mxgxw/reaccion/dsn/auxiliar/Prototipo0/Prototipo0-BreadBoard_bb.png

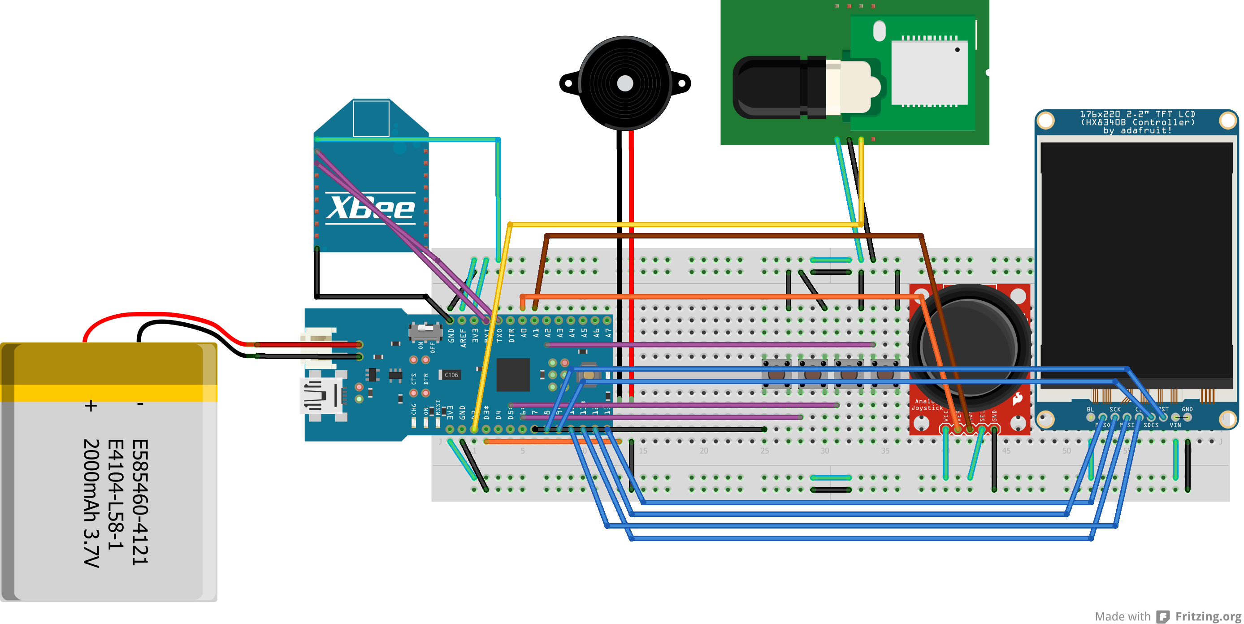
dsn/auxiliar/Prototipo0/Prototipo0-BreadBoard_bb.png
