mxgxw/reaccion/dsn/auxiliar/Prototipo0/Prototipo0-BreadBoard_esquema.png

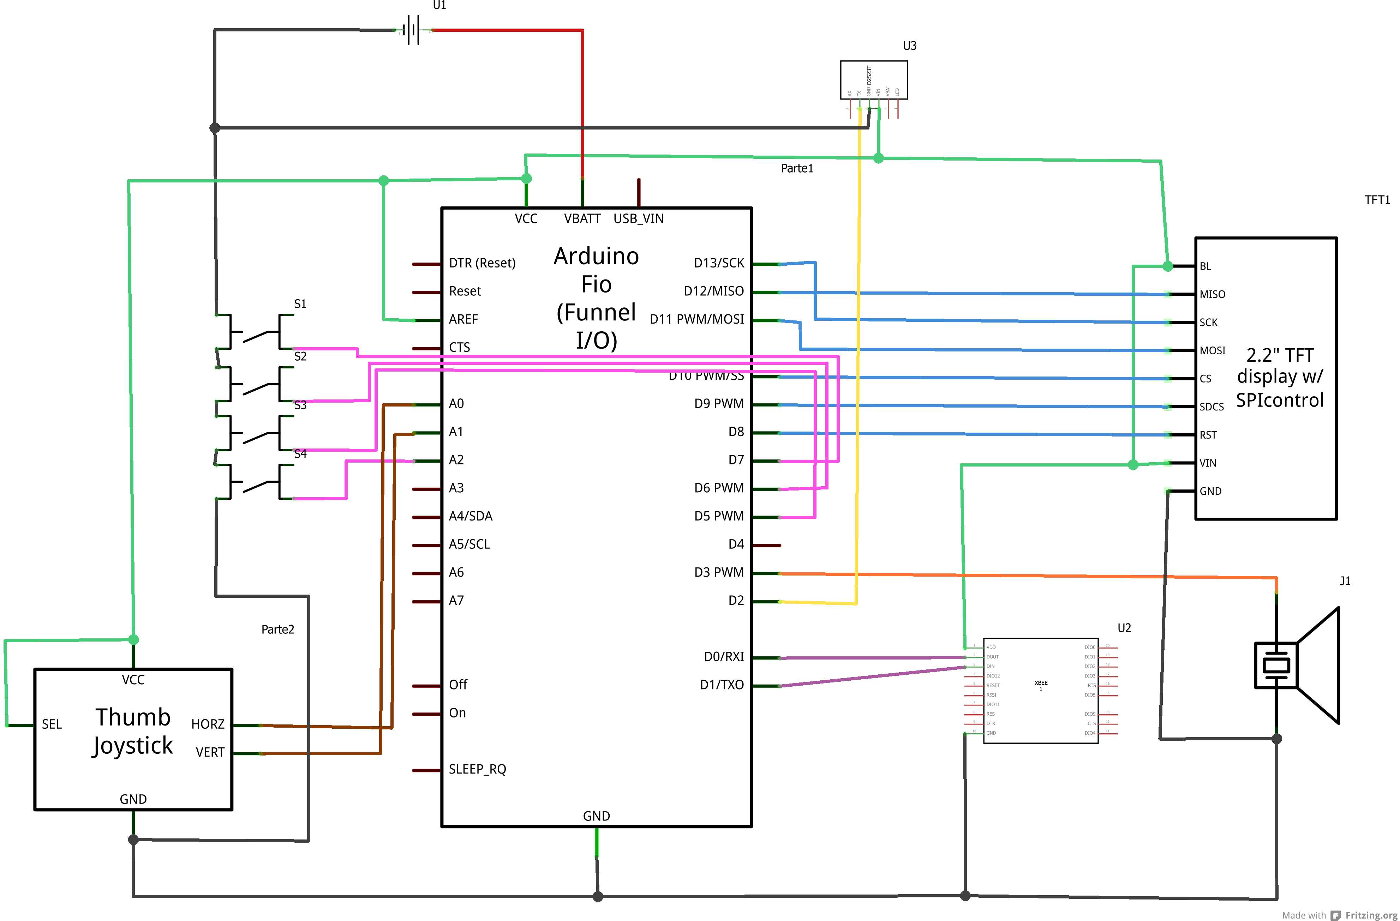
dsn/auxiliar/Prototipo0/Prototipo0-BreadBoard_esquema.png
