mxgxw/reaccion/dsn/main/Renders/Reaccion-01-BoardBottom.png

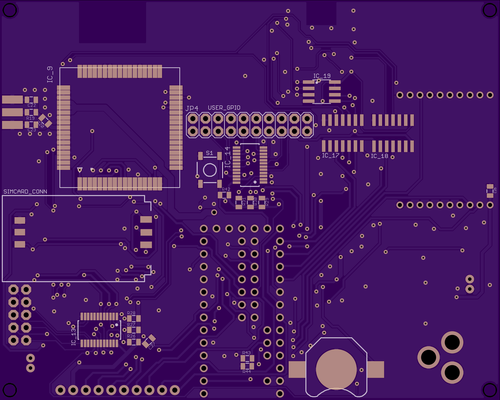
dsn/main/Renders/Reaccion-01-BoardBottom.png
