mxgxw/reaccion/dsn/main/Renders/Reaccion-04-TopLayer.png

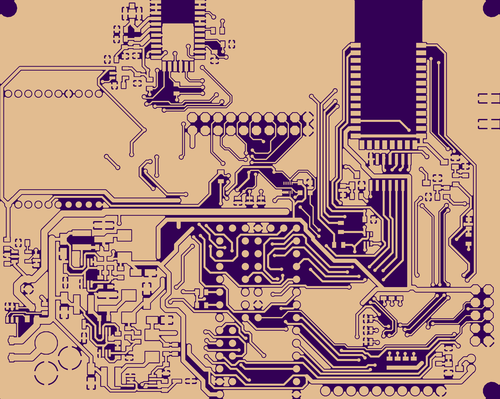
dsn/main/Renders/Reaccion-04-TopLayer.png
