mxgxw/reaccion/dsn/main/Renders/Reaccion-07-TopSilkScreen.png

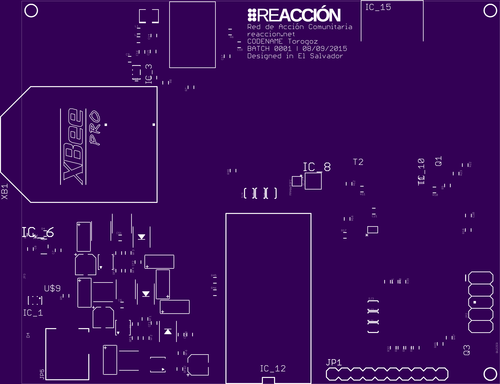
dsn/main/Renders/Reaccion-07-TopSilkScreen.png
