mxgxw/reaccion/extra/Graficos/0_skylab_20120524174805.jpg

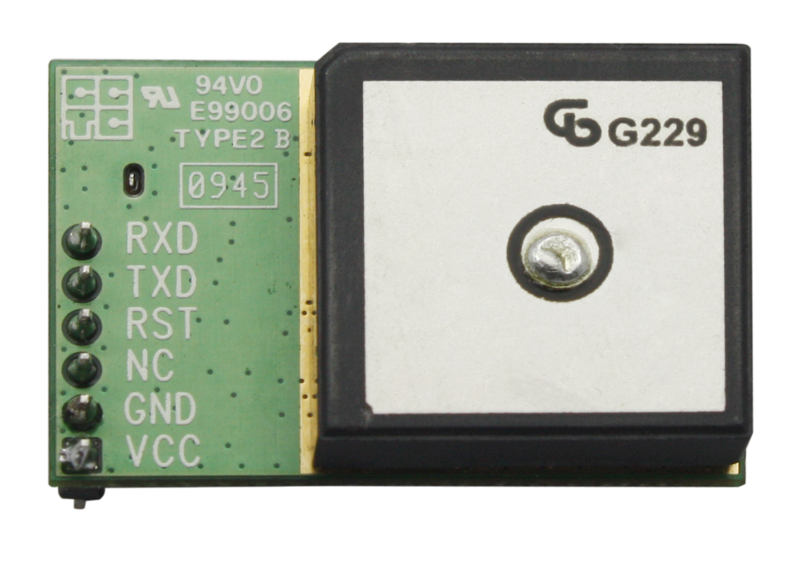
extra/Graficos/0_skylab_20120524174805.jpg
