mxgxw/reaccion/extra/Graficos/09099-01-L.jpg

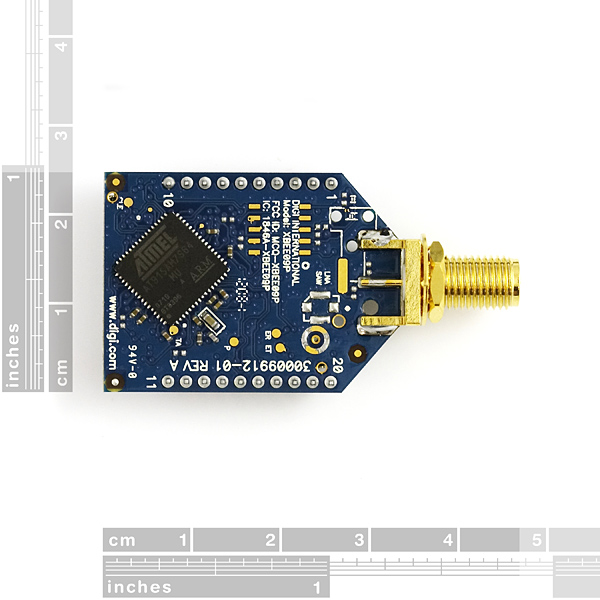
extra/Graficos/09099-01-L.jpg
