mxgxw/reaccion/extra/Graficos/board_top.png

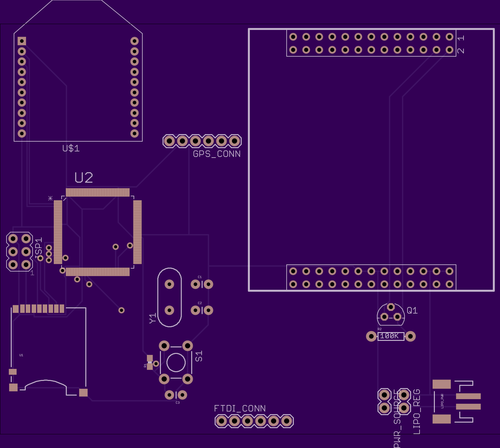
extra/Graficos/board_top.png
