mxgxw/reaccion/extra/Graficos/ET-AVR_Stamp_ATMega128_D.jpg

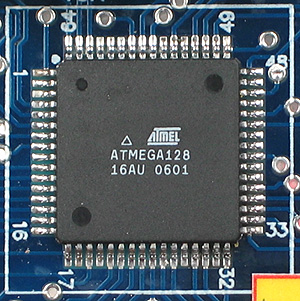
extra/Graficos/ET-AVR_Stamp_ATMega128_D.jpg
