mxgxw/reaccion/extra/Graficos/g3386.bmp

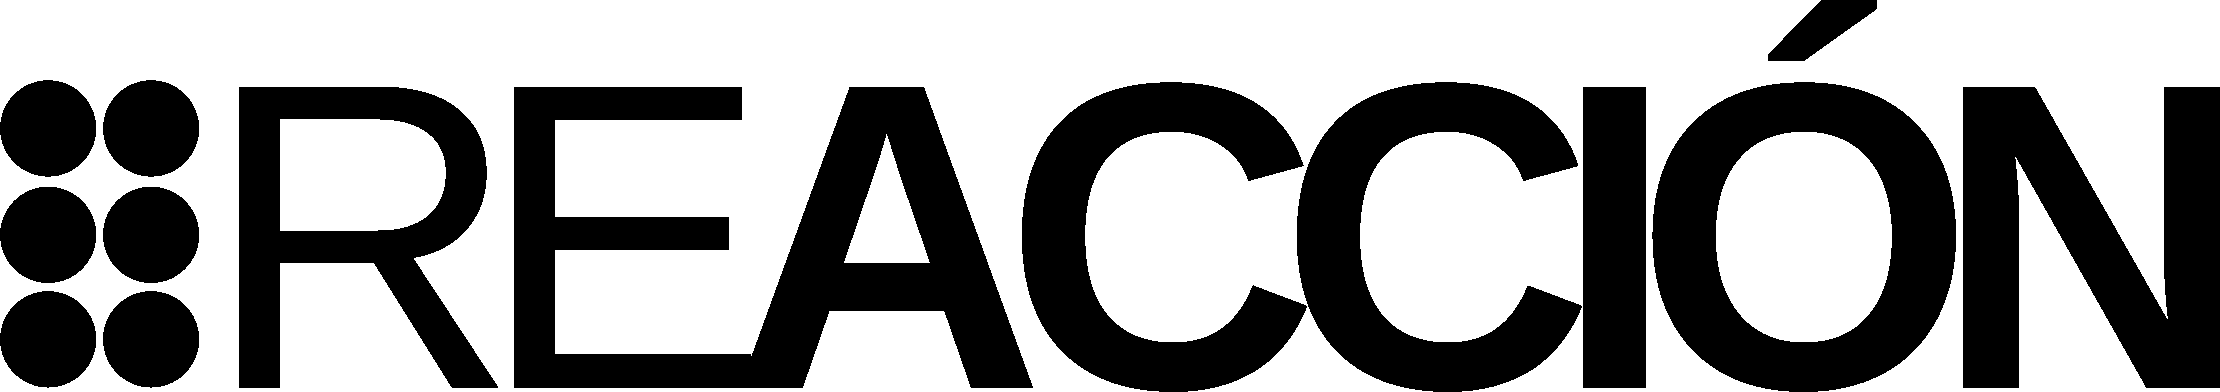
extra/Graficos/g3386.bmp
