mxgxw/reaccion/extra/Graficos/PARA WEB-Finales/1.jpg.png

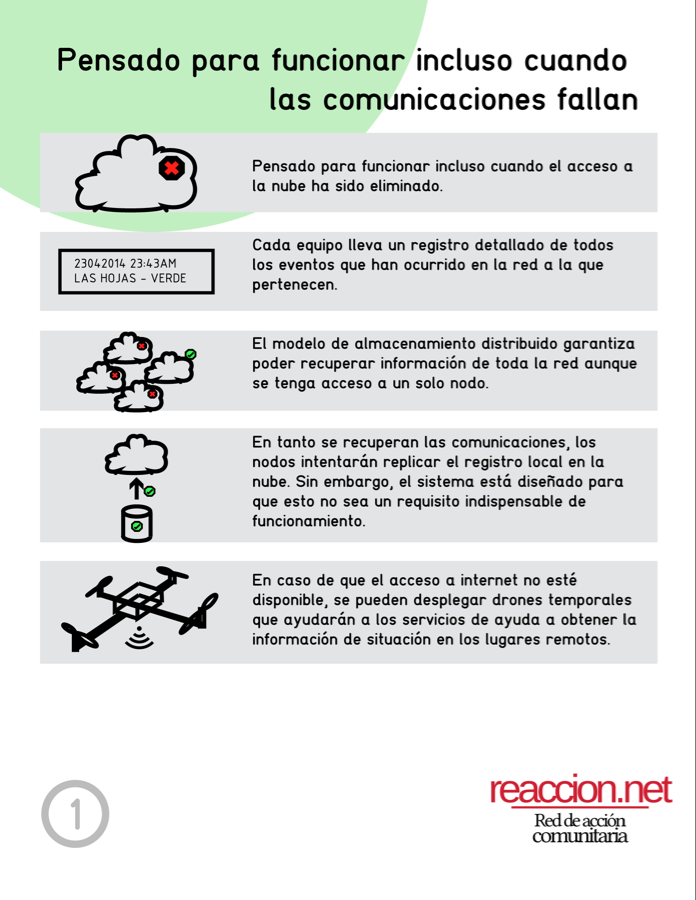
extra/Graficos/PARA WEB-Finales/1.jpg.png
