mxgxw/reaccion/extra/Graficos/PARA WEB-Finales/2.jpg.png

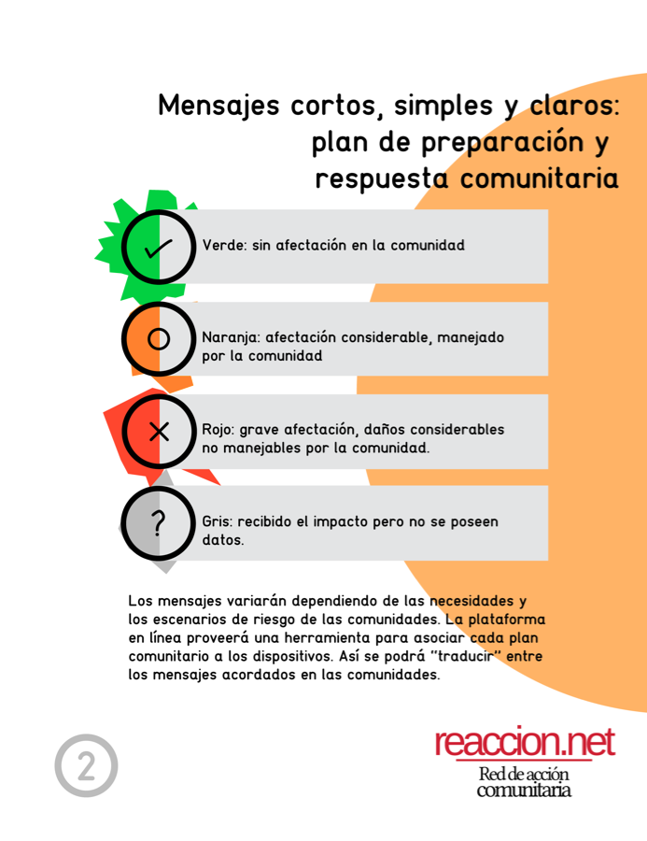
extra/Graficos/PARA WEB-Finales/2.jpg.png
