mxgxw/reaccion/extra/Graficos/PARA WEB-Finales/3.jpg.png

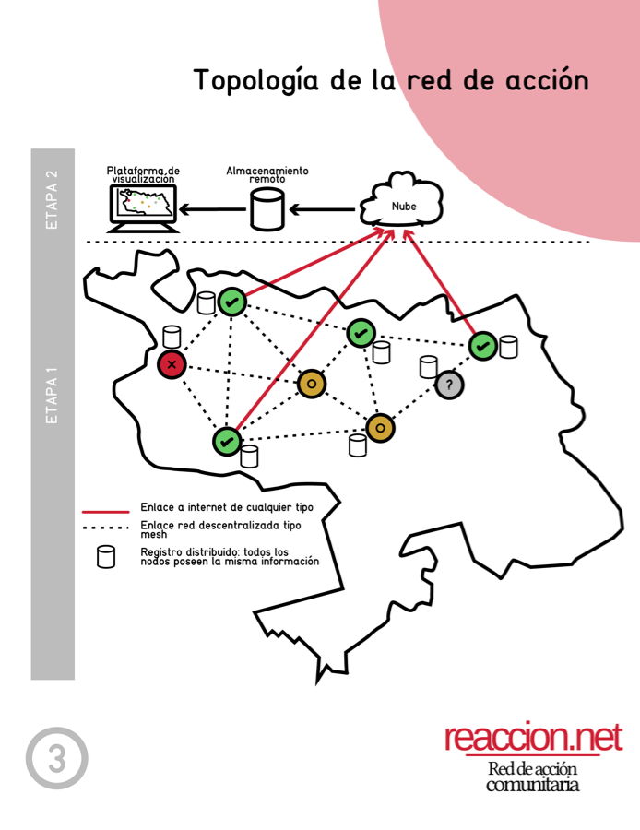
extra/Graficos/PARA WEB-Finales/3.jpg.png
