mxgxw/reaccion/extra/Graficos/PARA WEB-Finales/4.jpg

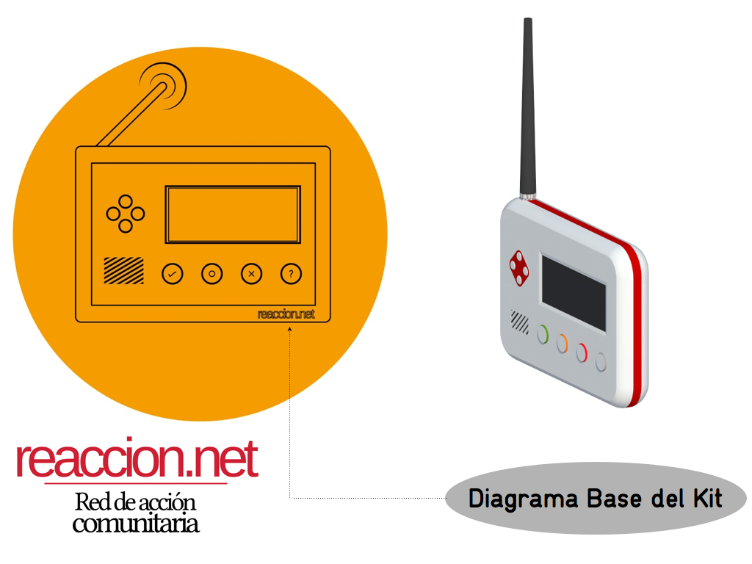
extra/Graficos/PARA WEB-Finales/4.jpg
