mxgxw/reaccion/extra/Graficos/PARA WEB-Finales/5.jpg

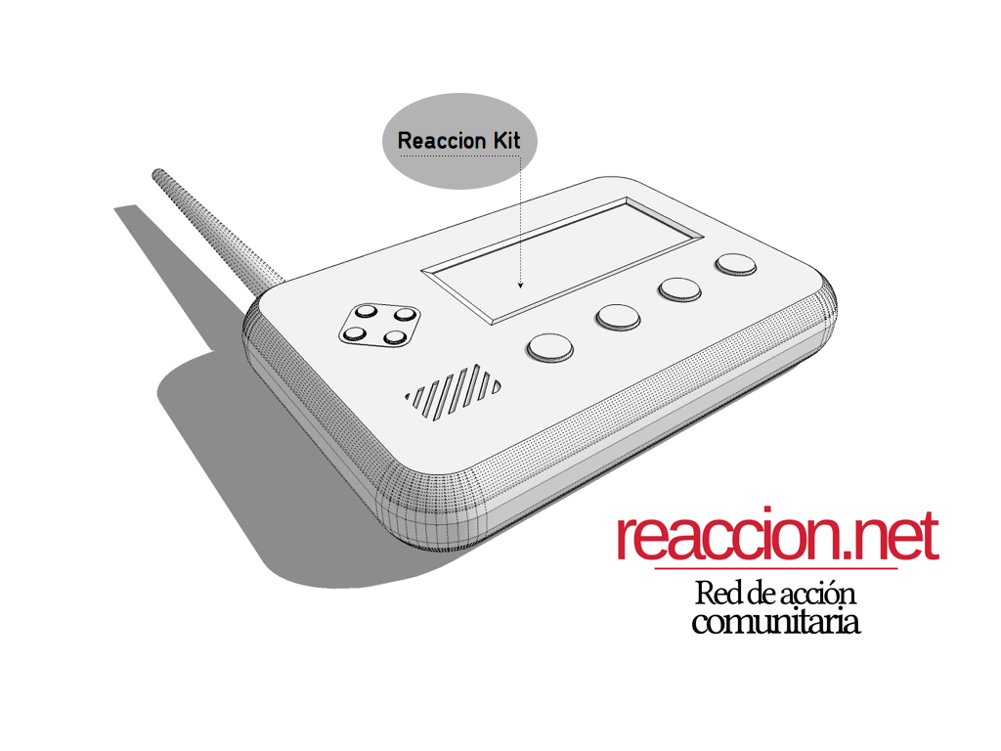
extra/Graficos/PARA WEB-Finales/5.jpg
