mxgxw/reaccion/extra/Graficos/PARA WEB-Finales/6.jpg

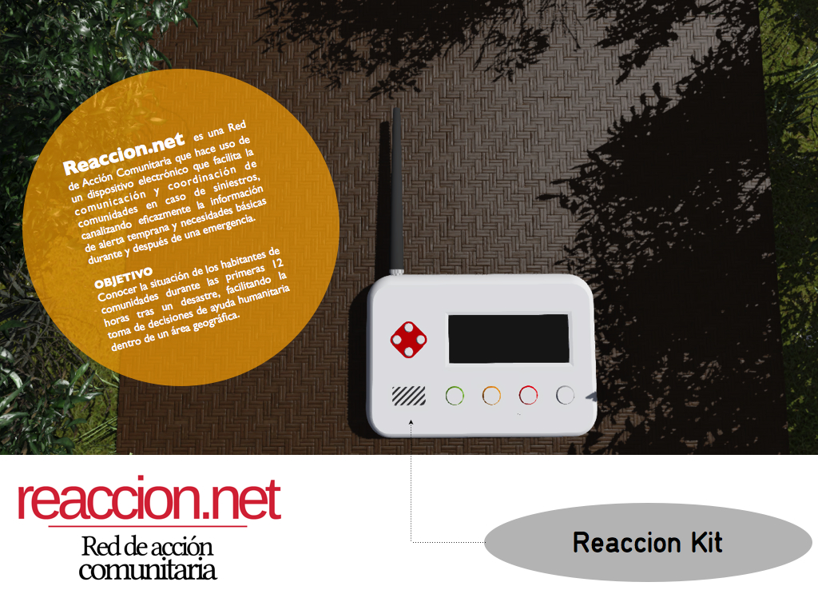
extra/Graficos/PARA WEB-Finales/6.jpg
