mxgxw/reaccion/extra/Graficos/PARA WEB-Finales/7.jpg

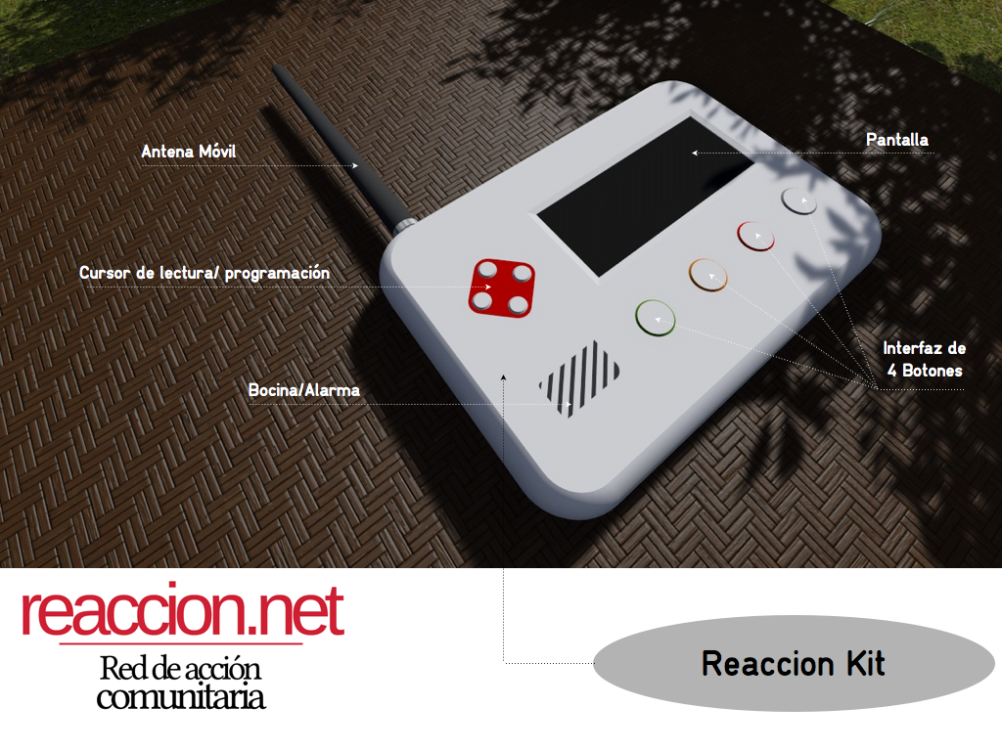
extra/Graficos/PARA WEB-Finales/7.jpg
