mxgxw/reaccion/extra/Graficos/teensy_and_button.jpg

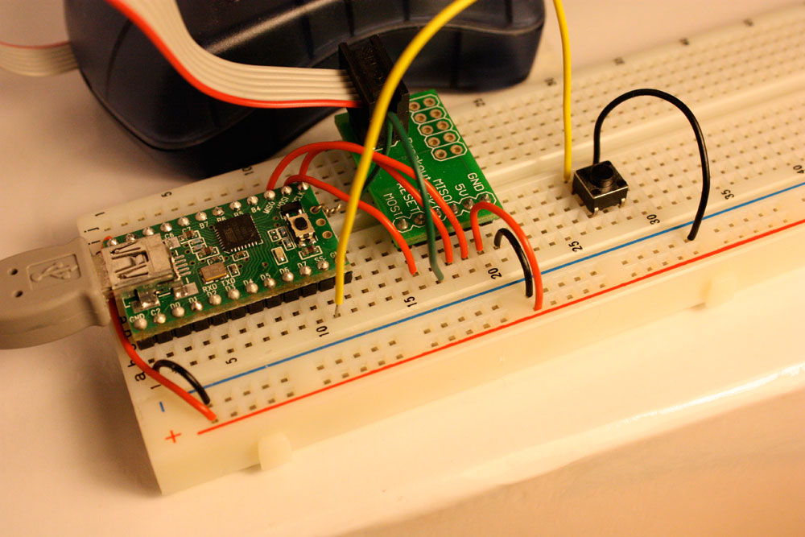
extra/Graficos/teensy_and_button.jpg
