mxgxw/reaccion/extra/Pasto/Board_Bottom.png

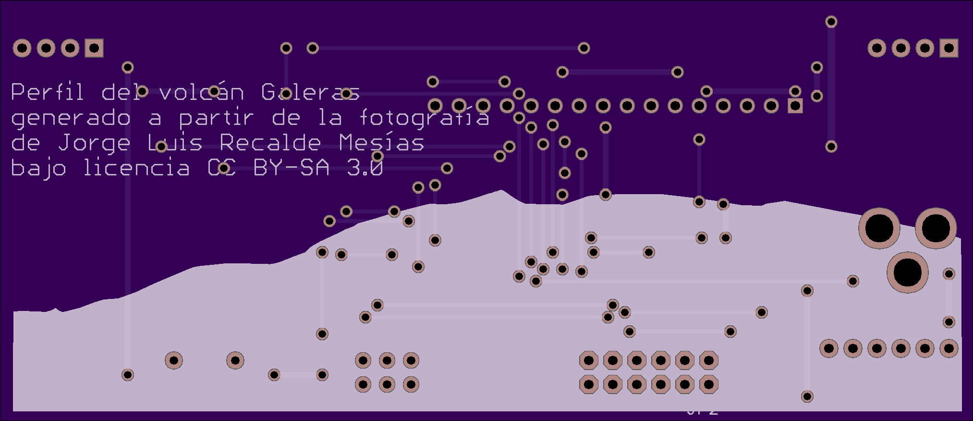
extra/Pasto/Board_Bottom.png
