mxgxw/reaccion/extra/Pasto/Board_Top.png

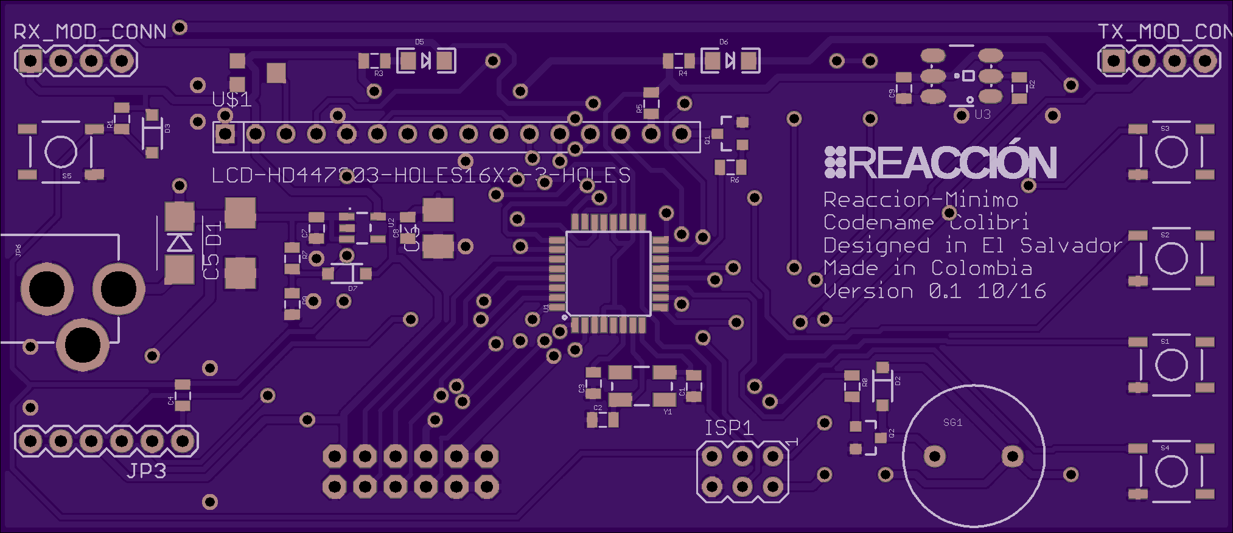
extra/Pasto/Board_Top.png
