mxgxw/reaccion/extra/Pasto/Galeras_ciudad.jpg

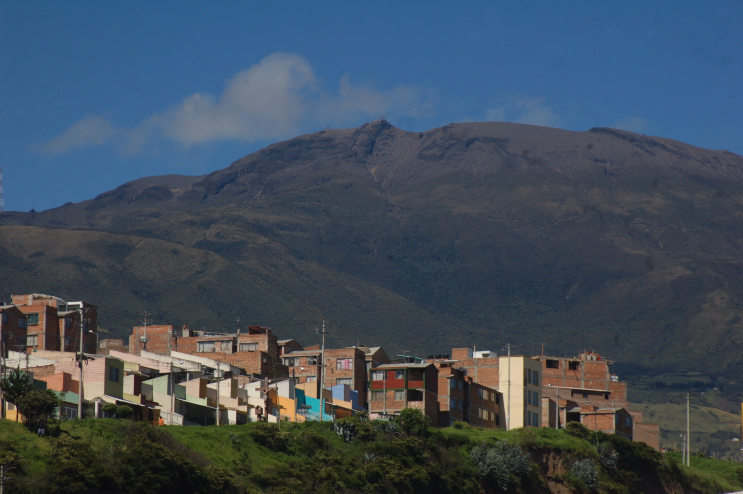
extra/Pasto/Galeras_ciudad.jpg
