mxgxw/reaccion/extra/Pasto/pcb.png

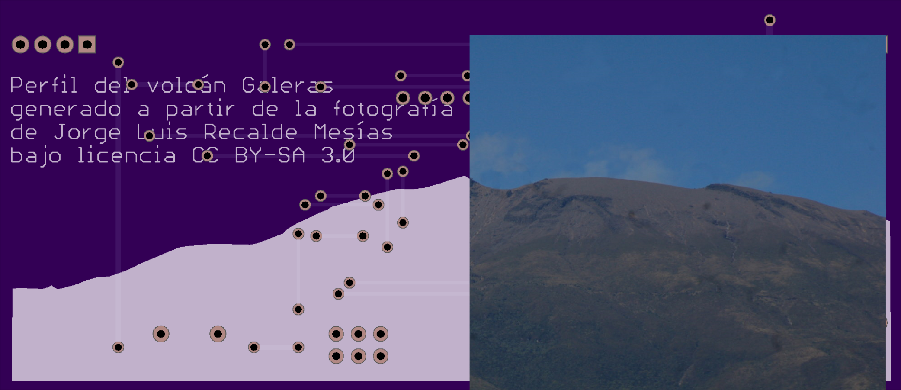
extra/Pasto/pcb.png
