mxgxw/reaccion/extra/sketchs/20140112-Sketch-Kako.jpg

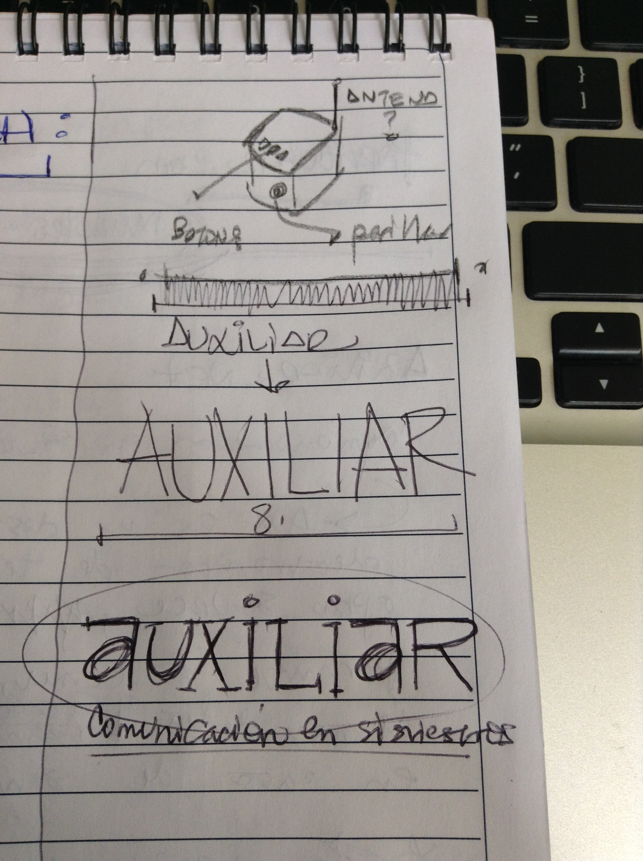
extra/sketchs/20140112-Sketch-Kako.jpg
