mxgxw/reaccion/extra/sketchs/Análisis del nombre a 30 votos.png

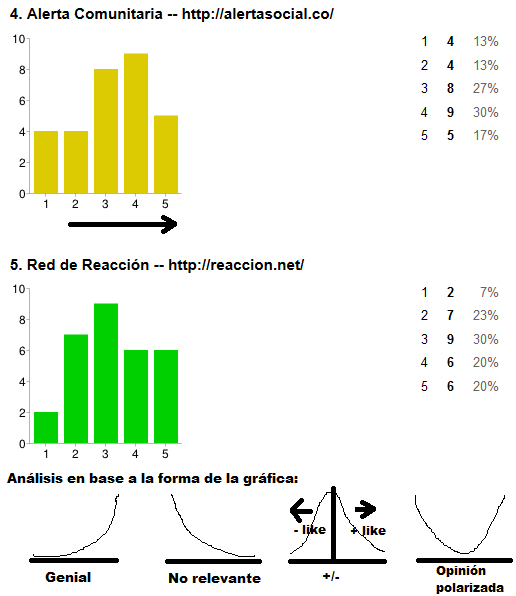
extra/sketchs/Análisis del nombre a 30 votos.png
