mxgxw/reaccion/extra/sketchs/Dispositivo.jpg

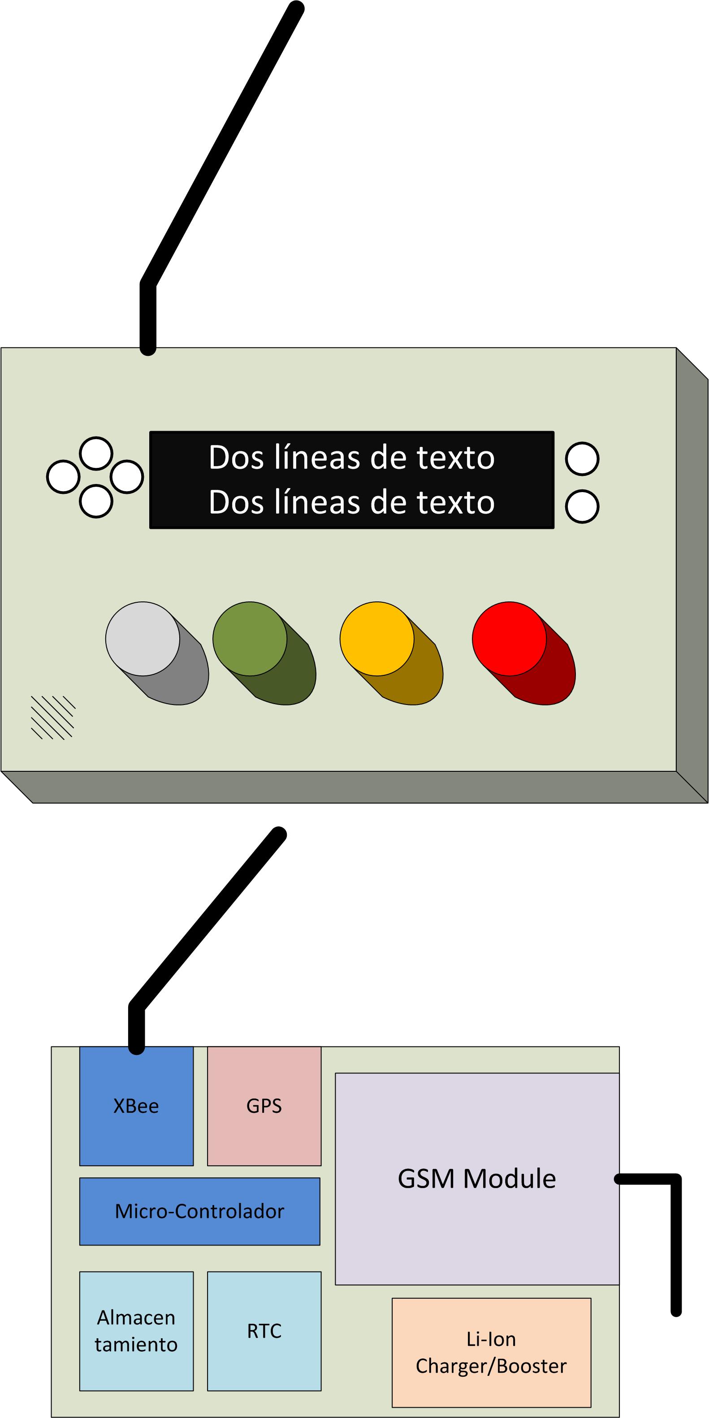
extra/sketchs/Dispositivo.jpg
