mxgxw/reaccion/dsn/main/Renders/Reaccion-03-TopSolderMask.png

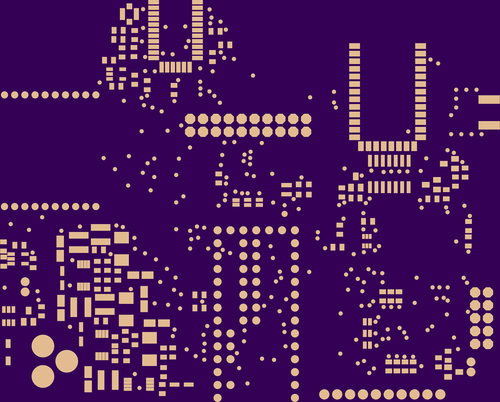
dsn/main/Renders/Reaccion-03-TopSolderMask.png
