mxgxw/reaccion/dsn/main/Renders/Reaccion-06-BottomSolderMask.png

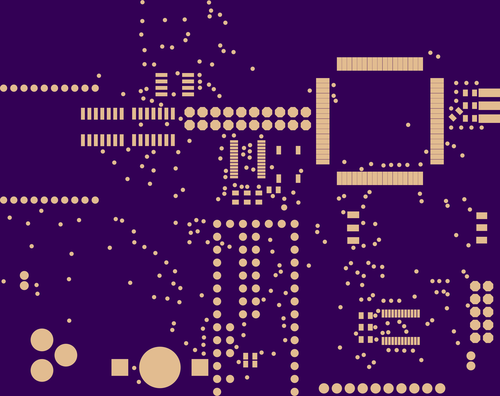
dsn/main/Renders/Reaccion-06-BottomSolderMask.png
