mxgxw/reaccion/src/LCD_TEST/LCD_TEST.ino

#include <Manchester.h>
#define BUFFER_SIZE 3
#define RX_PIN 6
int16_t data[BUFFER_SIZE];

// include the library code:
#include <LiquidCrystal.h>

// initialize the library with the numbers of the interface pins
LiquidCrystal lcd(8, 9, 2, 3, 4, 6);

void setup() {
  // set up the LCD's number of columns and rows:
  lcd.begin(16, 2);
}

void loop() {
  // set the cursor to (0,0):
  lcd.setCursor(0, 0);
  // print from 0 to 9:
  for (int thisChar = 0; thisChar < 10; thisChar++) {
    lcd.print(thisChar);
    delay(500);
  }

  // set the cursor to (16,1):
  lcd.setCursor(16, 1);
  // set the display to automatically scroll:
  lcd.autoscroll();
  // print from 0 to 9:
  for (int thisChar = 0; thisChar < 10; thisChar++) {
    lcd.print(thisChar);
    delay(500);
  }
  // turn off automatic scrolling
  lcd.noAutoscroll();

  // clear screen for the next loop:
  lcd.clear();
}
